gabe2001/PCLapCounterWithArduino/resources/PCLapCounter/PCLC_Options_Power-Control-&-Lights.png

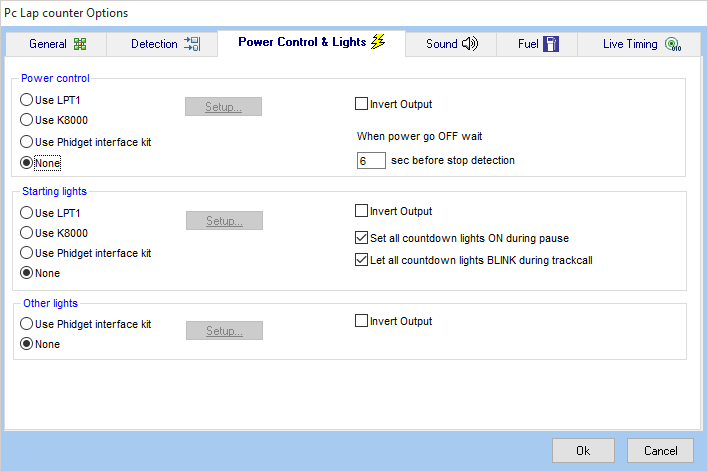
resources/PCLapCounter/PCLC_Options_Power-Control-&-Lights.png
